DMME-NL/RP2040-DSP-Public/src/effects/fuzz.h

/* fuzz.h
 * Author: Milan Wendt
 * Date:   2025-08-19
 *
 * Copyright (c) 2025 Milan Wendt
 *
 * This file is part of the RP2040-DSP project.
 *
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
 * You should have received a copy of the GNU General Public License along with this project. 
 * If not, see <https://www.gnu.org/licenses/>.
 */
#ifndef FUZZ_H
#define FUZZ_H

#include <stdint.h>

// --- fuzz parameters in Q8.24 ---
static int32_t fz_gain          = 0x01000000;
static int32_t fz_volume        = 0x01000000;
static int32_t fz_low_gain_q24  = 0x01000000;
static int32_t fz_mid_gain_q24  = 0x01000000;
static int32_t fz_mid_a_q24     = MID_A_Q24;
static int32_t fz_high_gain_q24 = 0x01000000;
static int32_t fz_asym_q24      = 0x01400000;  // ~1.25 in Q8.24 (more distortion on negative side)

// --- Filter states ---
static int32_t fz_low_state_l = 0, fz_mid_lp_state_l = 0, fz_mid_hp_state_l = 0, fz_high_state_l = 0;
static int32_t fz_low_state_r = 0, fz_mid_lp_state_r = 0, fz_mid_hp_state_r = 0, fz_high_state_r = 0;
static int32_t fz_lpf_state_l = 0, fz_lpf_state_r = 0;
static int32_t fz_hpf_state_l = 0, fz_hpf_state_r = 0;

// --- Optimized fuzz clip ---
static inline __attribute__((always_inline)) int32_t hard_clip(int32_t x) {
    if (x >  0x300000) x =  0x300000;      // ~0.1875
    if (x < -0x300000) x = -0x300000;

    // Fast x^2 in reduced precision (as you had)
    int32_t xr = x >> 12;
    int32_t x2 = xr * xr;                  // non-Q24, intentional

    if (x >= 0) {
        // was: return (x - (x2 >> 13)) * 8;
        int32_t soft = x - (x2 >> 13);
        return soft * 8;
    } else {
        // was:
        // int64_t bias_term = ((int64_t)x2 << 24) / fz_asym_q24;
        // return (x + (int32_t)(bias_term >> 13)) * 8;

        // Rounded divide: ((num) / fz_asym_q24) with sign-aware 0.5 LSB
        int64_t num = ((int64_t)x2 << 24);
        int64_t den = (int64_t)fz_asym_q24;
        if (num >= 0) num += (den >> 1); else num -= (den >> 1);
        int32_t bias_q24 = (int32_t)(num / den);  // Q8.24
        int32_t bias = bias_q24 >> 13;            // match your original scaling
        return (x + bias) * 8;
    }
}

// --- Per-channel fuzz processing ---
static inline __attribute__((always_inline)) int32_t process_fz_channel(
    int32_t s,
    int32_t *low_state,
    int32_t *mid_lp_state,
    int32_t *mid_hp_state,
    int32_t *high_state,
    int32_t *lpf_state,
    int32_t *hpf_state
) {
    // Gain
    // was: s = (int32_t)(((int64_t)s * fz_gain) >> 24);
    s = qmul(s, fz_gain);

    // HPF before clipping to reduce rumble
    s = apply_1pole_hpf(s, hpf_state, HPF_A_Q24);   // Global HPF

    // Clipping
    s = hard_clip(s);

    // LPF after clipping to reduce fizz
    s = apply_1pole_lpf(s, lpf_state, LPF_A_Q24);   // Global LPF

    // Low-shelf
    int32_t low_out = apply_1pole_lpf(s, low_state, BASS_A_Q24); // Global BASS
    // was: low_out = (int32_t)(((int64_t)low_out * fz_low_gain_q24) >> 24);
    low_out = qmul(low_out, fz_low_gain_q24);

    // Mid band-pass
    int32_t mid_band = apply_1pole_lpf(
        apply_1pole_hpf(s, mid_hp_state, fz_mid_a_q24),
        mid_lp_state, fz_mid_a_q24
    );
    // was: mid_out = (int32_t)(((int64_t)mid_band * fz_mid_gain_q24) >> 24);
    int32_t mid_out = qmul(mid_band, fz_mid_gain_q24);

    // High-shelf filter
    int32_t high_out = s - apply_1pole_lpf(s, high_state, TREBLE_A_Q24); // Global TREB
    // was: high_out = (int32_t)(((int64_t)high_out * fz_high_gain_q24) >> 24);
    high_out = qmul(high_out, fz_high_gain_q24);

    // Final volume scale (round collapse once)
    int64_t y = (int64_t)low_out + (int64_t)mid_out + (int64_t)high_out;
    y = y * (int64_t)fz_volume;
    y += (y >= 0) ? (1LL<<23) : -(1LL<<23);   // round-to-nearest
    int32_t output = clamp24((int32_t)(y >> 24));
    return output;
}

// --- Process stereo sample ---
static inline void process_audio_fuzz_sample(int32_t* inout_l, int32_t* inout_r, bool stereo) {
    *inout_l = process_fz_channel(*inout_l, &fz_low_state_l, &fz_mid_lp_state_l, &fz_mid_hp_state_l, &fz_high_state_l, &fz_lpf_state_l, &fz_hpf_state_l);
    if(!stereo){    *inout_r = *inout_l; } // Process MONO
    else{           *inout_r = process_fz_channel(*inout_r, &fz_low_state_r, &fz_mid_lp_state_r, &fz_mid_hp_state_r, &fz_high_state_r, &fz_lpf_state_r, &fz_hpf_state_r); }
}

// --- Load parameters ---
static inline void load_fuzz_parms_from_memory(void) {
    int32_t pot;

    // Gain from -26dB to 0dB
    pot = storedPotValue[FZ_EFFECT_INDEX][0];
    fz_gain          = map_pot_to_q24(pot, float_to_q24(0.05f), float_to_q24(1.0f));

    // Bass from -12dB to +6dB
    pot = storedPotValue[FZ_EFFECT_INDEX][1];
    fz_low_gain_q24  = map_pot_to_q24(pot, float_to_q24(0.25f), float_to_q24(2.0f));

    // Mid from -12dB to +9.5dB
    pot = storedPotValue[FZ_EFFECT_INDEX][2];
    fz_mid_gain_q24  = map_pot_to_q24(pot, float_to_q24(0.25f), float_to_q24(3.0f));

    // Mid frequency: 400 Hz to 1 kHz
    pot = storedPotValue[FZ_EFFECT_INDEX][3];
    fz_mid_a_q24 = map_pot_to_q24(pot, 0x0009F15A, 0x001F68E3);

    // Treb from -12dB to +6dB
    pot = storedPotValue[FZ_EFFECT_INDEX][4];
    fz_high_gain_q24 = map_pot_to_q24(pot, float_to_q24(0.25f), float_to_q24(2.0f));

    // Volume from -6dB to +28dB
    pot = storedPotValue[FZ_EFFECT_INDEX][5];
    fz_volume        = map_pot_to_q24(pot, float_to_q24(0.5f), float_to_q24(26.0f));

    fz_low_state_l = fz_mid_lp_state_l = fz_mid_hp_state_l = fz_high_state_l = 0;
    fz_low_state_r = fz_mid_lp_state_r = fz_mid_hp_state_r = fz_high_state_r = 0;
    fz_lpf_state_l = fz_lpf_state_r = 0;
    fz_hpf_state_l = fz_hpf_state_r = 0;
}

// --- Update from UI ---
static inline void update_fuzz_params_from_pots(int changed_pot) {
    if (changed_pot < 0 || changed_pot > 5) return;
    storedPotValue[FZ_EFFECT_INDEX][changed_pot] = pot_value[changed_pot];
    load_fuzz_parms_from_memory();
}

void fuzz_process_block(int32_t* in_l, int32_t* in_r, size_t frames, bool stereo) {
    for (size_t i = 0; i < frames; i++) {
        process_audio_fuzz_sample(&in_l[i], &in_r[i], stereo);
    }
}

#endif // FUZZ_H
